JavierCasatorres/infrarred_gun/3D_designs/trigger_support.SLDPRT

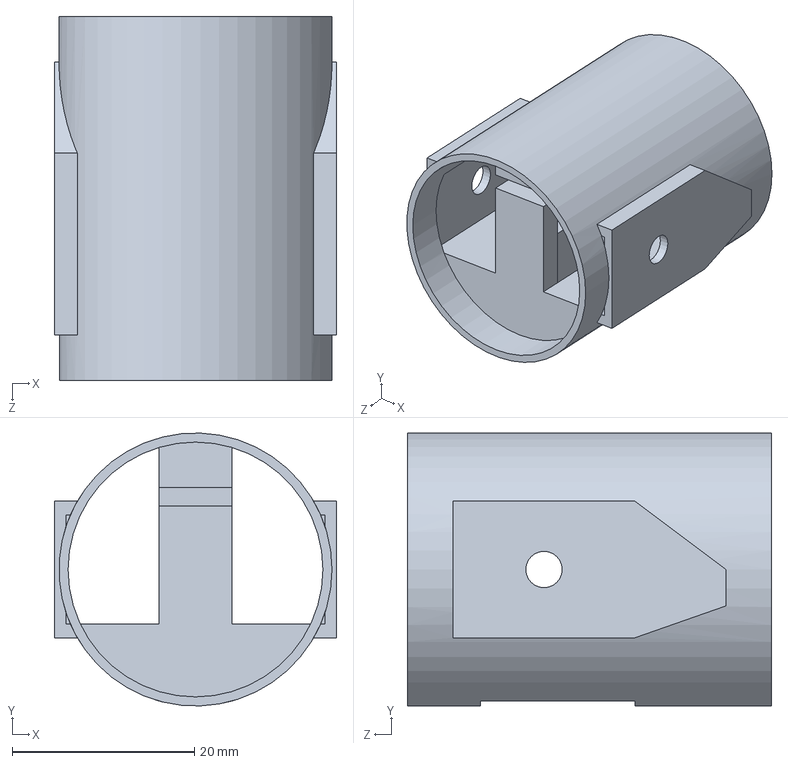
[picture p15: CAD file, 2021-11-10, an earlier design]
3D_designs/trigger_support.SLDPRT
31.0 x 30.0 x 40.0 mm
